shouryashashank/Awesome-H-shifter/awesome-H-shifter.sch

## EAGLE design awesome-H-shifter.sch (2025-12-25)

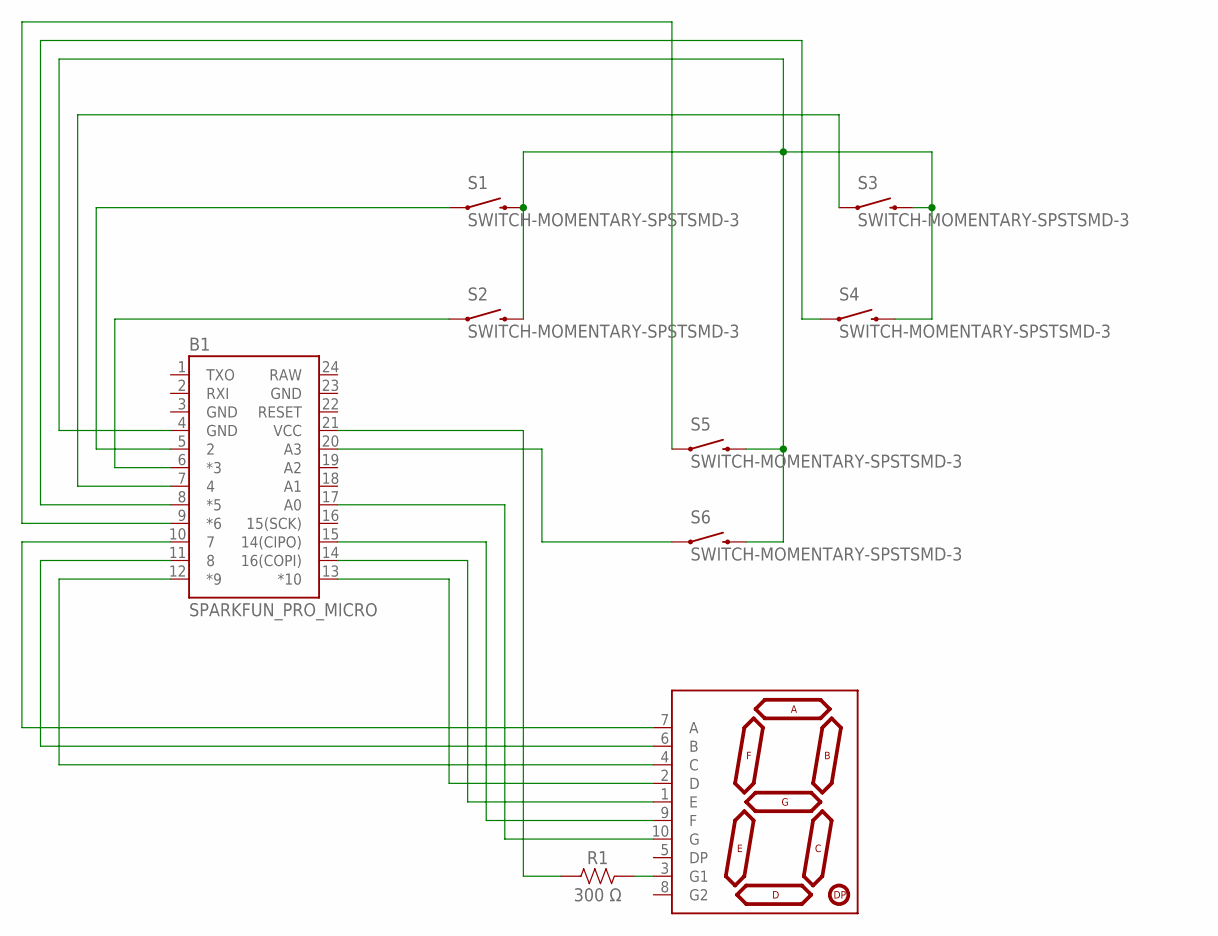
[picture p13: schematic awesome-H-shifter.sch]

Parts:
B1: SPARKFUN_PRO_MICRO
R1: 300 Ω; RESC1005X40
S1, S2, S3, S4, S5, S6: SWITCH-MOMENTARY-SPSTSMD-3; TACTILE_SWITCH_SMD-3
U$1: 7-SEGMENT-DISPLAYPTH; 7-SEGMENT-DISPLAY

Connections:
unnamed: B1.4 (GND), S1.4 (2), S2.4 (2), S3.4 (2), S4.4 (2), S5.4 (2), S6.4 (2)
unnamed: B1.5 (2), S1.1
unnamed: B1.6 (*3), S2.1
unnamed: B1.7 (4), S3.1
unnamed: B1.8 (*5), S4.1
unnamed: B1.9 (*6), S5.1
unnamed: B1.10 (7), U$1.7 (A)
unnamed: B1.11 (8), U$1.6 (B)
unnamed: B1.12 (*9), U$1.4 (C)
unnamed: B1.13 (*10), U$1.2 (D)
unnamed: B1.14 (16(COPI)), U$1.1 (E)
unnamed: B1.15 (14(CIPO)), U$1.9 (F)
unnamed: B1.17 (A0), U$1.10 (G)
unnamed: B1.21 (VCC), R1.1
unnamed: B1.20 (A3), S6.1
unnamed: R1.2, U$1.3 (G1)
